knspektrum/jammer/firmware/utils.h

#ifndef UTILS_H
#define UTILS_H

#define COUNT_OF(x)                                                            \
  ((sizeof(x) / sizeof(0 [x])) / ((size_t)(!(sizeof(x) % sizeof(0 [x])))))

#define SWAP(x, y) (x ^= y ^= x ^= y)

#endif
